hermahs/Sureloc/models/Shelf module/Frame Clip Tool.stl

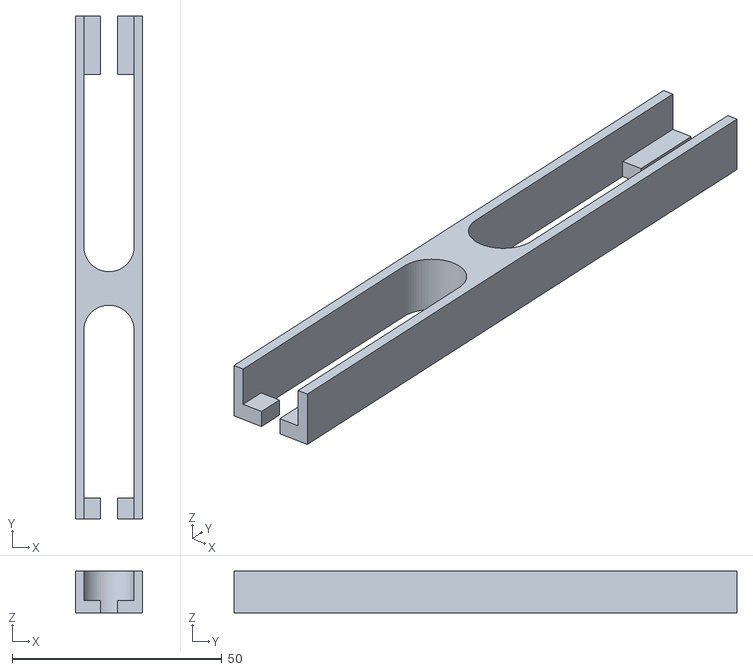
[picture p17: CAD file, 2023-05-08]
models/Shelf module/Frame Clip Tool.stl
16.0 x 120.0 x 10.0
