hermahs/Sureloc/models/Shelf module/Clip Thick.stl

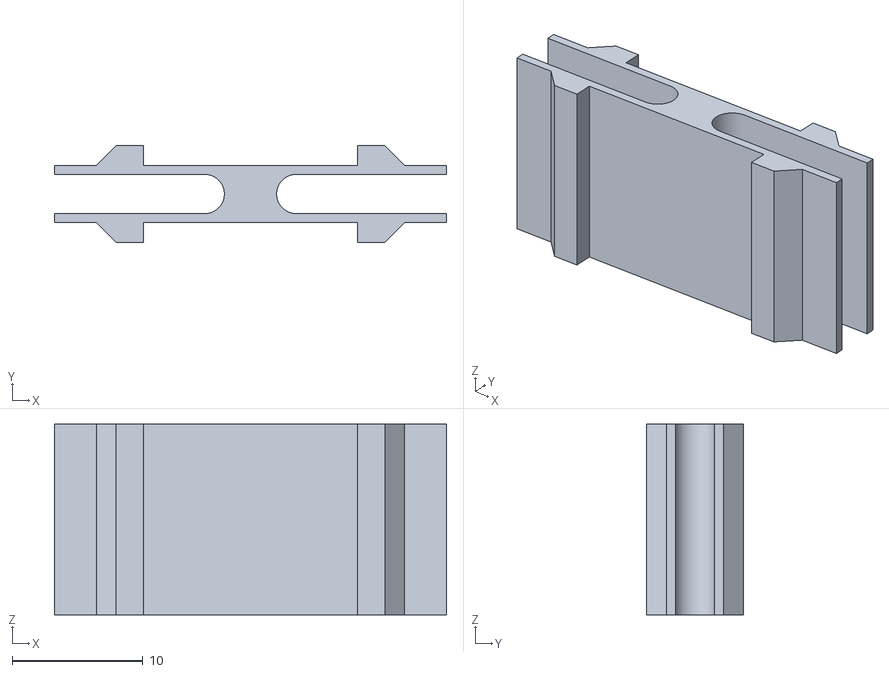
[picture p18: CAD file, 2023-05-08]
models/Shelf module/Clip Thick.stl
30.0 x 7.40 x 14.6
