hermahs/Sureloc/models/Shelf module/Wall Mount Rail.stl

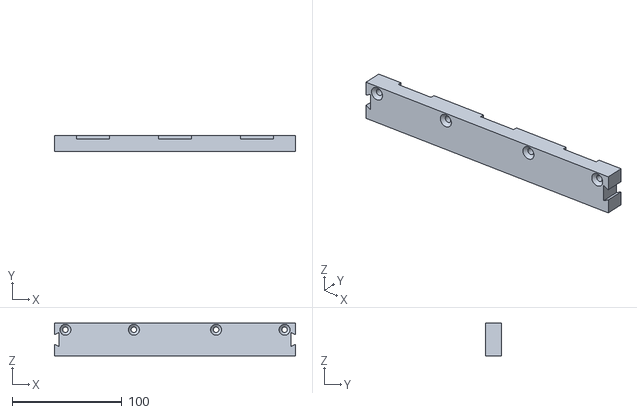
[picture p19: CAD file, 2023-05-08]
models/Shelf module/Wall Mount Rail.stl
220.0 x 14.8 x 29.8
