hermahs/Sureloc/models/Shelf module/Back stop.stl

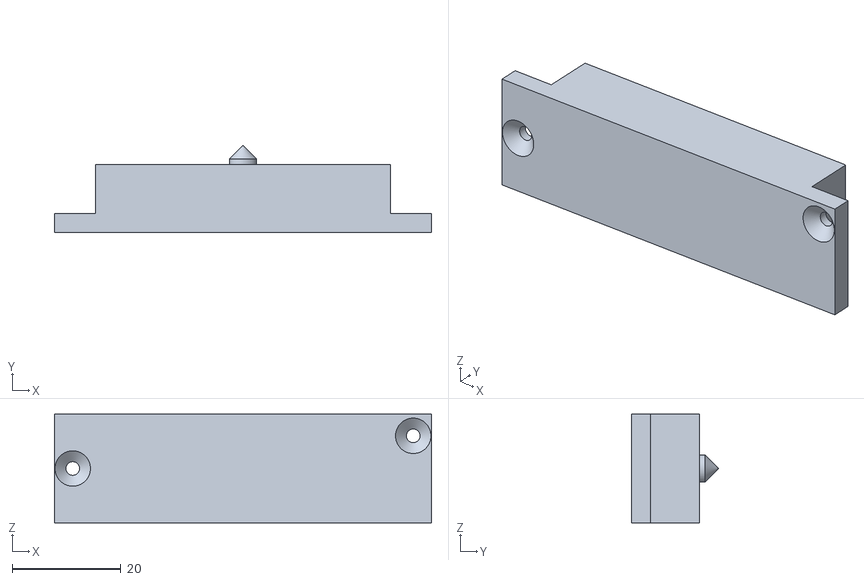
[picture p20: CAD file, 2023-05-08]
models/Shelf module/Back stop.stl
69.2 x 16.0 x 20.0
