hermahs/Sureloc/models/Shelf module/Rail Loadcell.stl

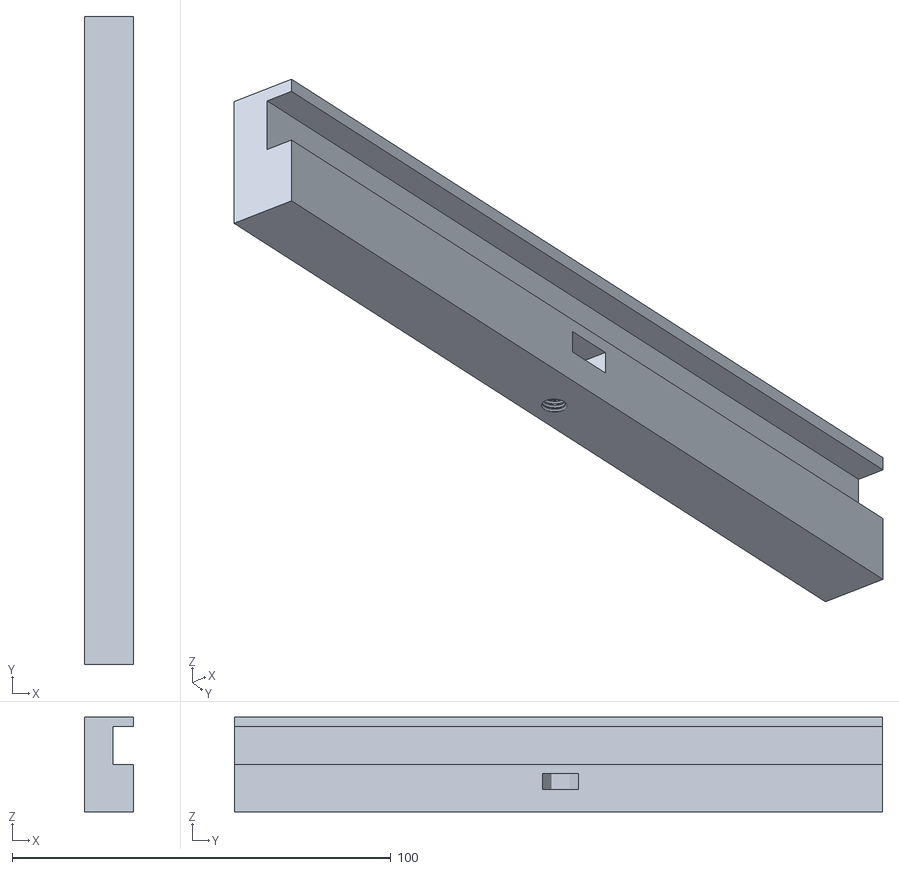
[picture p21: CAD file, 2023-05-08]
models/Shelf module/Rail Loadcell.stl
13.0 x 171.0 x 25.0
