hermahs/Sureloc/models/Shelf module/Drawer Rail.stl

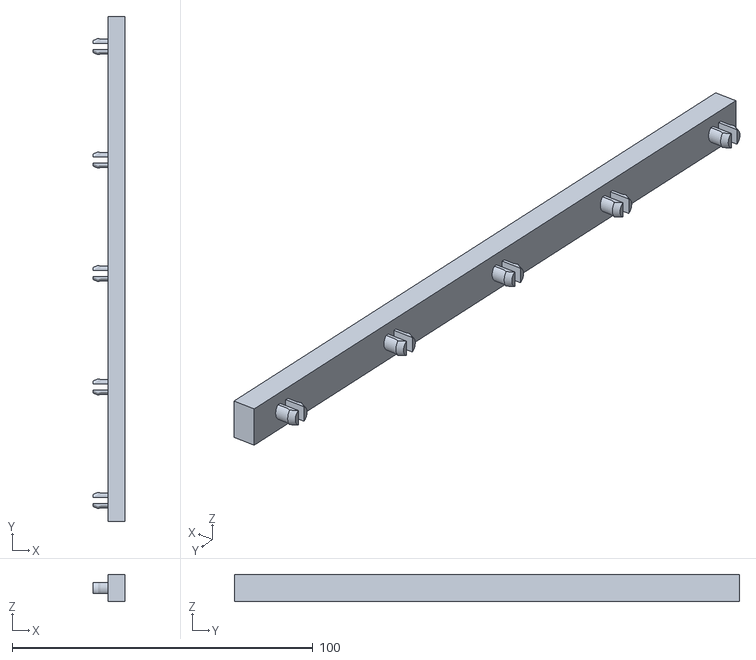
[picture p22: CAD file, 2023-05-08]
models/Shelf module/Drawer Rail.stl
10.5 x 168.0 x 9.00
