hermahs/Sureloc/scripts/ControlBox/commands.h

// box commands
#define ACK 0x00
#define OPEN 0x01
#define CLOSE 0x02
#define NEW 0x03
#define CALIBRATE 0x04
#define WEIGHT 0x05

// controller commands
#define OK 0x98
#define NOT_OK 0x99

#define AVAILABLE HIGH
